RJSent/stm8_card/media/20210215_150121.jpg

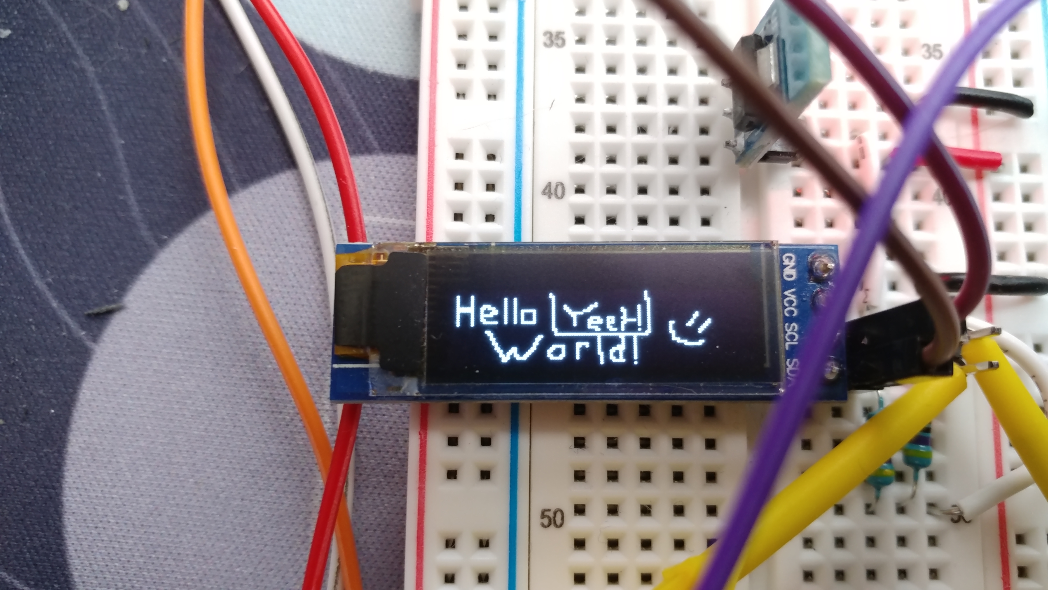
media/20210215_150121.jpg
